cl-ei/GameKunV1/Software/h723_gk_from_7a3/Core/Inc/custom/cxk.c

#include "cxk.h"

const uint16_t cxk_data[17580] = {0x0000, 0x0000, 0x0200, 0x03FF, 0x03FF, 0x03CF, 0x03CF, 0x0383, 0x0380, 0x0000, 0x0000, 0x0000, 0x0000, 0x0000, 0x0200, 0x03E7, 0x03FF, 0x03CF, 0x03CD, 0x03C5, 0x03C0, 0x0000, 0x0000, 0x0000, 0x0000, 0x0000, 0x0200, 0x03E7, 0x03FF, 0x03CF, 0x03CD, 0x03C5, 0x03C0, 0x0000, 0x0000, 0x0000, 0x0000, 0x0000, 0x0200, 0x03C7, 0x03FF, 0x03CD, 0x03CD, 0x03C3, 0x03C0, 0x0000, 0x0000, 0x0000, 0x0000, 0x0000, 0x0200, 0x03C7, 0x03FF, 0x03CD, 0x03CD, 0x03C3, 0x03C0, 0x0000, 0x0000, 0x0000, 0x0000, 0x0000, 0x0200, 0x03C7, 0x03FF, 0x03CD, 0x03CD, 0x03C3, 0x03C0, 0x0000, 0x0000, 0x0000, 0x0000, 0x0000, 0x0200, 0x0383, 0x03FD, 0x03CD, 0x03CF, 0x03C3, 0x03D8, 0x0000, 0x0000, 0x0000, 0x0000, 0x0000, 0x0200, 0x0383, 0x03FD, 0x03CD, 0x03CF, 0x03C3, 0x03D8, 0x0000, 0x0000, 0x0000, 0x0000, 0x0000, 0x0200, 0x0383, 0x03FF, 0x03CD, 0x03CF, 0x03DB, 0x03D8, 0x0000, 0x0000, 0x0000, 0x0000, 0x0000, 0x0200, 0x0383, 0x03FF, 0x03CD, 0x03CF, 0x03DB, 0x03D8, 0x0000, 0x0000, 0x0000, 0x0000, 0x0000, 0x0200, 0x0383, 0x03FF, 0x03CF, 0x03CF, 0x03DB, 0x0398, 0x0000, 0x0000, 0x0000, 0x0000, 0x0000, 0x0200, 0x0383, 0x03FF, 0x03CF, 0x03CF, 0x03DB, 0x0398, 0x0000, 0x0000, 0x0000, 0x0000, 0x0000, 0x0200, 0x0383, 0x03FF, 0x03CF, 0x03CF, 0x03DB, 0x0398, 0x0000, 0x0000, 0x0000, 0x0000, 0x0000, 0x0200, 0x03C3, 0x03FF, 0x03CF, 0x03CF, 0x03D9, 0x03D0, 0x0000, 0x0000, 0x0000, 0x0000, 0x0000, 0x0200, 0x03C3, 0x03FF, 0x03CF, 0x03CF, 0x03D9, 0x03D0, 0x0000, 0x0000, 0x0000, 0x0000, 0x0000, 0x0200, 0x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
