cl-ei/GameKunV1/Software/h723_gk_from_7a3/Core/Inc/custom/myt.h

#ifndef __MY_TYPES_H
#define __MY_TYPES_H

#ifdef __cplusplus
extern "C" {
#endif

#include "stm32h7xx_hal.h"

typedef uint64_t u64;
typedef uint32_t u32;
typedef uint16_t u16;
typedef uint8_t u8;

typedef int64_t i64;
typedef int32_t i32;
typedef int16_t i16;
typedef int8_t i8;

#ifdef __cplusplus
}
#endif

#endif
